arigato-java/RealJavaButton/images/examples-ver1_0_0-03.jpg

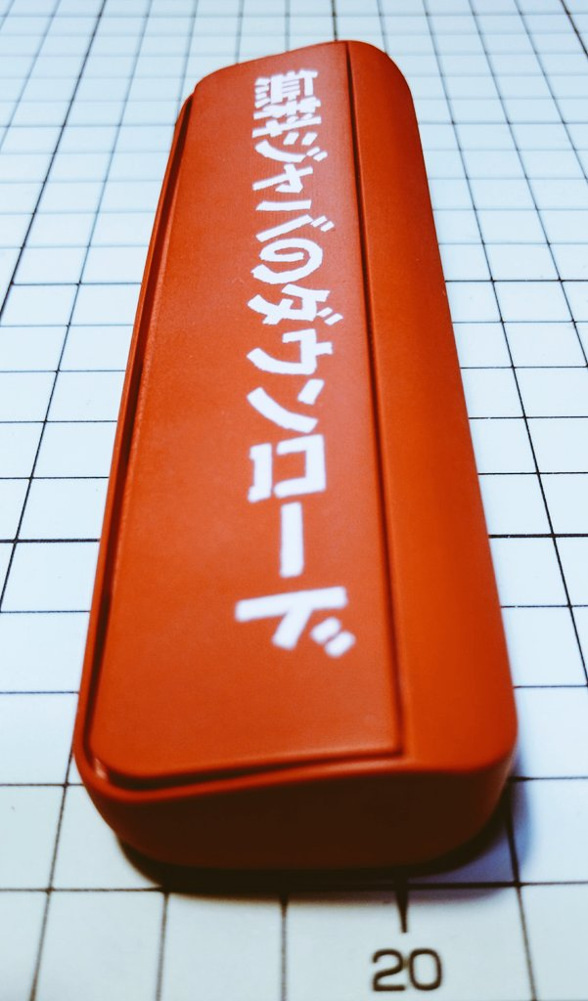
images/examples-ver1_0_0-03.jpg
