arigato-java/RealJavaButton/images/examples-ver1_0_0-label01.jpg

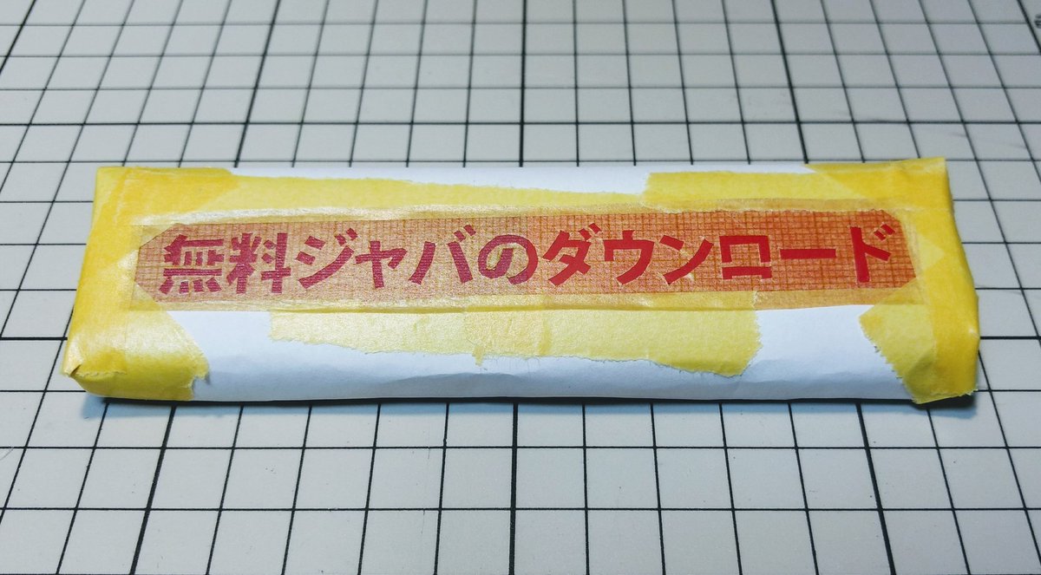
images/examples-ver1_0_0-label01.jpg
