arigato-java/RealJavaButton/schematic/main.sch

## KiCad design schematic/main.sch (2017-08-19)

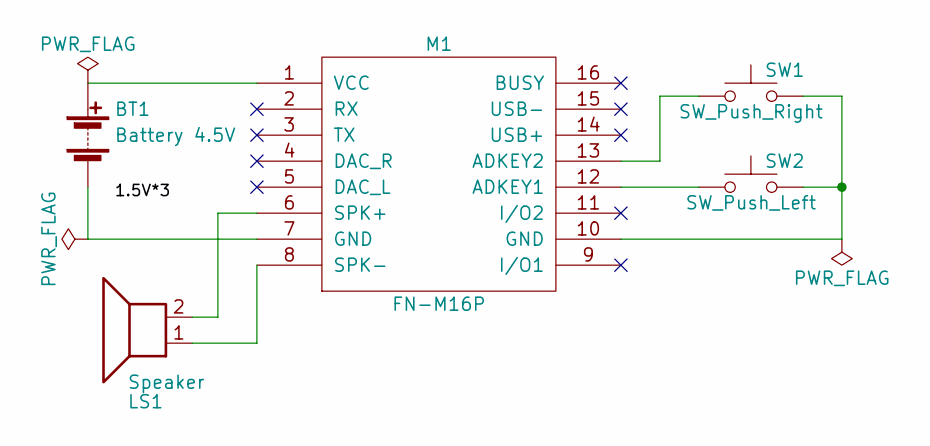
[picture p21: schematic main.sch]

Parts:
BT1: Battery 4.5V
LS1: Speaker
M1: FN-M16P
SW1: SW_Push_Right
SW2: SW_Push_Left

Connections:
unnamed: BT1.1 (+), M1.1 (VCC)
unnamed: BT1.2 (-), M1.7 (GND)
unnamed: LS1.1, M1.8 (SPK-)
unnamed: LS1.2, M1.6 (SPK+)
unnamed: M1.10 (GND), SW1.2, SW2.2
unnamed: M1.12 (ADKEY1), SW2.1
unnamed: M1.13 (ADKEY2), SW1.1
